3d-paws/3D-PAWS-Feather-LoRa-Remote/FeatherLoRaRemote/SM.h

/*
 * ======================================================================================================================
 * StationMonitor() - When Jumper set Display StationMonitor()
 * ======================================================================================================================
 */

 /*
 * ======================================================================================================================
 * StationMonitor() - On OLED display station information
 * ======================================================================================================================
 */
void StationMonitor() {
  static int cycle = 0;
  static int count = 0;
  static int b = 0;
  static int p = 0;  // use to loop through each probe 0,1,2
  int r, c, len;
  
  OLED_ClearDisplayBuffer();

  DoSoilReadings(); // Get Soil Moisture and temperature readings
  
  float batt = vbat_get();

  // =================================================================
  // Line 0 of OLED   [Timestamp]
  // =================================================================
  rtc_timestamp();
  len = (strlen (timestamp) > 21) ? 21 : strlen (timestamp);
  for (c=0; c<=len; c++) oled_lines [0][c] = *(timestamp+c);
  Serial_write (timestamp);

  // =================================================================
  // Line 1 of OLED
  // =================================================================
  if (cf_ds_enable) {
    int sg  = (int) analogRead(DISTANCE_GAUGE_PIN) * cf_ds_enable;  // cf_ds_enable = 0,5,10
    sprintf (msgbuf, "SG:%d %s", sg, (cf_ds_enable) ? "10m" : "5m"); 
  }
  else {
    sprintf (msgbuf, "SG:NF");
  }
  len = (strlen (msgbuf) > 21) ? 21 : strlen (msgbuf);
  for (c=0; c<=len; c++) oled_lines [1][c] = *(msgbuf+c);
  Serial_write (msgbuf);
  
  // =================================================================
  // Line 2 of OLED
  // =================================================================
  if (cf_rg1_enable) {
    sprintf (msgbuf, "RG1:%d", (int) raingauge1_interrupt_count);
  }
  else {
    sprintf (msgbuf, "RG1:NF");
  }
  
  if (cf_rg2_enable) {
    sprintf (msgbuf+strlen(msgbuf), " RG2:%d", (int) raingauge2_interrupt_count);
  }
  else {
    sprintf (msgbuf+strlen(msgbuf), " RG2:NF");
  }
  len = (strlen (msgbuf) > 21) ? 21 : strlen (msgbuf);
  for (c=0; c<=len; c++) oled_lines [2][c] = *(msgbuf+c);
  Serial_write (msgbuf);

  // =================================================================
  // Line 3 of OLED Cycle between multiple sensors
  // =================================================================
  if (cycle == 0) {
    if (BMX_1_exists) {
      float bmx_pressure = 0.0;
      float bmx_temp = 0.0;
      float bmx_humid;
      
      switch (BMX_1_chip_id) {
        case BMP280_CHIP_ID :
          bmx_pressure = bmp1.readPressure()/100.0F;           // bmxp1
          bmx_temp = bmp1.readTemperature();                   // bmxt1
          break;
        
        case BME280_BMP390_CHIP_ID :
          if (BMX_1_chip_id == BME280_BMP390_CHIP_ID) {
            bmx_pressure = bme1.readPressure()/100.0F;           // bmxp1
            bmx_temp = bme1.readTemperature();                   // bmxt1
            bmx_humid = bme1.readHumidity();                     // bmxh1 
          }
          else { // BMP390
            bmx_pressure = bm31.readPressure()/100.0F;
            bmx_temp = bm31.readTemperature();
          }
          break;
          
        case BMP388_CHIP_ID :
          bmx_pressure = bm31.readPressure()/100.0F;
          bmx_temp = bm31.readTemperature();
          break;
        
        default: // WTF
          break;
      }
      sprintf (msgbuf, "B1 %d.%02d %d.%02d %d.%02d", 
        (int)bmx_pressure, (int)(bmx_pressure*100)%100,
        (int)bmx_temp, (int)(bmx_temp*100)%100,
        (int)bmx_humid, (int)(bmx_humid*100)%100);
    }
    else {
      sprintf (msgbuf, "B1 NF");
    }
  }
  
  if (cycle == 1) {
    if (BMX_2_exists) {
      float bmx_pressure = 0.0;
      float bmx_temp = 0.0;
      float bmx_humid;
      
      switch (BMX_2_chip_id) {
        case BMP280_CHIP_ID :
          bmx_pressure = bmp2.readPressure()/100.0F;           // bmxp1
          bmx_temp = bmp1.readTemperature();                   // bmxt1
          break;
        
        case BME280_BMP390_CHIP_ID :
          if (BMX_2_chip_id == BME280_BMP390_CHIP_ID) {
            bmx_pressure = bme2.readPressure()/100.0F;           // bmxp1
            bmx_temp = bme1.readTemperature();                   // bmxt1
            bmx_humid = bme1.readHumidity();                     // bmxh1 
          }
          else { // BMP390
            bmx_pressure = bm32.readPressure()/100.0F;
            bmx_temp = bm31.readTemperature();
          }
          break;
          
        case BMP388_CHIP_ID :
          bmx_pressure = bm32.readPressure()/100.0F;
          bmx_temp = bm31.readTemperature();
          break;
        
        default: // WTF
          break;
      }
      sprintf (msgbuf, "B2 %d.%02d %d.%02d %d.%02d", 
        (int)bmx_pressure, (int)(bmx_pressure*100)%100,
        (int)bmx_temp, (int)(bmx_temp*100)%100,
        (int)bmx_humid, (int)(bmx_humid*100)%100);
    }
    else {
      sprintf (msgbuf, "B2 NF");
    }
  }

  if (cycle == 2) {
    memset(msgbuf, 0, sizeof(msgbuf));
      
    if (MCP_1_exists) {
      float mcp_temp = mcp1.readTempC();   
      sprintf (msgbuf, "MCP1 T%d.%02d", (int)mcp_temp, (int)(mcp_temp*100)%100);
    }
    else {
      sprintf (msgbuf, "MCP1 NF");
    }
  }

  if (cycle == 3) {
    if (MCP_2_exists) {
      float mcp_temp = mcp2.readTempC();   
      sprintf (msgbuf, "MCP2 T%d.%02d", (int)mcp_temp, (int)(mcp_temp*100)%100);
    }
    else {
      sprintf (msgbuf, "MCP2 NF");
    }
  }

  if (cycle == 4) {
    if (SHT_1_exists) {
      float t = sht1.readTemperature();
      float h = sht1.readHumidity();
      sprintf (msgbuf, "SHT1 T:%d.%02d H:%d.%02d", 
         (int)t, (int)(t*100)%100,
         (int)h, (int)(h*100)%100);
    }
    else {
      sprintf (msgbuf, "SHT1 NF");
    }
  }

  if (cycle == 5) {
    if (SHT_2_exists) {
      float t = sht2.readTemperature();
      float h = sht2.readHumidity();
      sprintf (msgbuf, "SHT2 T:%d.%02d H:%d.%02d", 
         (int)t, (int)(t*100)%100,
         (int)h, (int)(h*100)%100);
    }
    else {
      sprintf (msgbuf, "SHT2 NF");
    }      
  }

  if (cycle == 6) {
    if (ds_found[0] || ds_found[1]) {
      sprintf (msgbuf, "S %d M:%d T:%d.%02d", 
        p+1, sm_reading[p], 
        (int)ds_reading[p], (int)(ds_reading[p]*100)%100);
      
      p = (++p) % NPROBES;
    }
    else {
      sprintf (msgbuf, "No Soil Moisture");
    }
  }

  if (cycle == 7) {
    sprintf (msgbuf, "B:%d.%02d H:%04X", 
    (int)batt, (int)(batt*100)%100, SystemStatusBits); 
  }

/*
  if (cycle == X) {   
    if (HTU21DF_exists) {
      float htu_humid = htu.readHumidity();
      float htu_temp = htu.readTemperature();

      sprintf (msgbuf, "HTU H:%02d.%02d T:%02d.%02d", 
        (int)htu_humid, (int)(htu_humid*100)%100, 
        (int)htu_temp, (int)(htu_temp*100)%100);
    }
    else {
      sprintf (msgbuf, "HTU NF"); 
    } 
  }
  
  if (cycle == X) {   
    if (VEML7700_exists) {
      float lux = veml.readLux(VEML_LUX_AUTO);
      lux = (isnan(lux)) ? 0.0 : lux;
        sprintf (msgbuf, "LX L%02d.%1d", (int)lux, (int)(lux*10)%10);
    }
    else {
      sprintf (msgbuf, "LX NF");
    }
  }
  
  if (cycle == X) {
    if (SI1145_exists) {
      float si_vis = uv.readVisible();
      float si_ir = uv.readIR();
      float si_uv = uv.readUV()/100.0;
      sprintf (msgbuf, "SI V%d.%02d I%d.%02d U%d.%02d", 
        (int)si_vis, (int)(si_vis*100)%100,
        (int)si_ir, (int)(si_ir*100)%100,
        (int)si_uv, (int)(si_uv*100)%100);
    }
    else {
      sprintf (msgbuf, "SI NF");
    }
  }
*/

  len = (strlen (msgbuf) > 21) ? 21 : strlen (msgbuf);
  for (c=0; c<=len; c++) oled_lines [3][c] = *(msgbuf+c);
  Serial_writeln (msgbuf);

  // Give the use some time to read line 3 before changing
  if (count++ >= 5) {
    cycle = ++cycle % 8; // << +1
    count = 0;
  }
  
  OLED_update();
}
