3d-paws/3D-PAWS-Feather-LoRa-Remote/FeatherLoRaRemote/include/eeprom.h

/*
 * ======================================================================================================================
 *  eeprom.h - EEPROM Definations
 * ======================================================================================================================
 */

/*
 * ======================================================================================================================
 *  EEPROM NonVolitileMemory - stores rain totals in persistant memory
 * ======================================================================================================================
 */
#define EEPROM_I2C_ADDR 0x50

typedef struct {
    float    rgt1;       // rain gauge total today
    float    rgp1;       // rain gauge total prior
    float    rgt2;       // rain gauge 2 total today
    float    rgp2;       // rain gauge 2 total prior
    uint32_t rgts;       // rain gauge timestamp of last modification
    unsigned long n2sfp; // sd need 2 send file position
    unsigned long checksum;
} EEPROM_NVM;

// Extern variables
extern EEPROM_NVM eeprom;
extern bool eeprom_valid;
extern bool eeprom_exists;

// Function prototype
unsigned long EEPROM_ChecksumCompute();
void EEPROM_ChecksumUpdate();
bool EEPROM_ChecksumValid();
void EEPROM_ClearRainTotals(uint32_t current_time);
bool EEPROM_TimeToRollOver();
void EEPROM_Validate();
void EEPROM_UpdateRainTotals(float rgt1, float rgt2);
void EEPROM_SaveUnreportedRain();
void EEPROM_Update();
void EEPROM_Dump();
void EEPROM_initialize();
