3d-paws/3D-PAWS-Feather-LoRa-Remote/FeatherLoRaRemote/include/info.h

/*
 * ======================================================================================================================
 *  info.h - Station Information Definations
 * ======================================================================================================================
 */

// Function prototypes
void INFO_Do();
