3d-paws/3D-PAWS-Feather-LoRa-Remote/FeatherLoRaRemote/include/statmon.h

/*
 * ======================================================================================================================
 *  statmon.h - Station Monitor Definations
 * ======================================================================================================================
 */

// Extern variables

// Function prototypes
void StationMonitor();
